sparkfun/SparkFun_Qwiic_6DoF_BMI270/docs/assets/imgs/22397_1.jpg

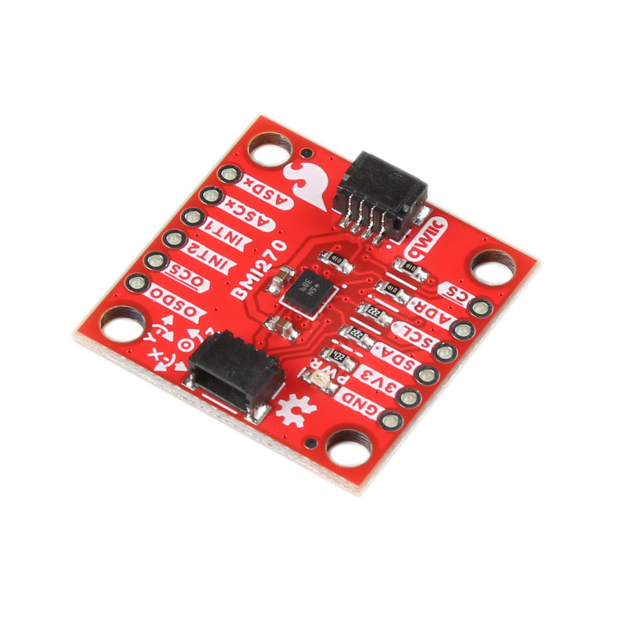
docs/assets/imgs/22397_1.jpg
