sparkfun/SparkFun_Qwiic_6DoF_BMI270/docs/assets/imgs/22397_3.jpg

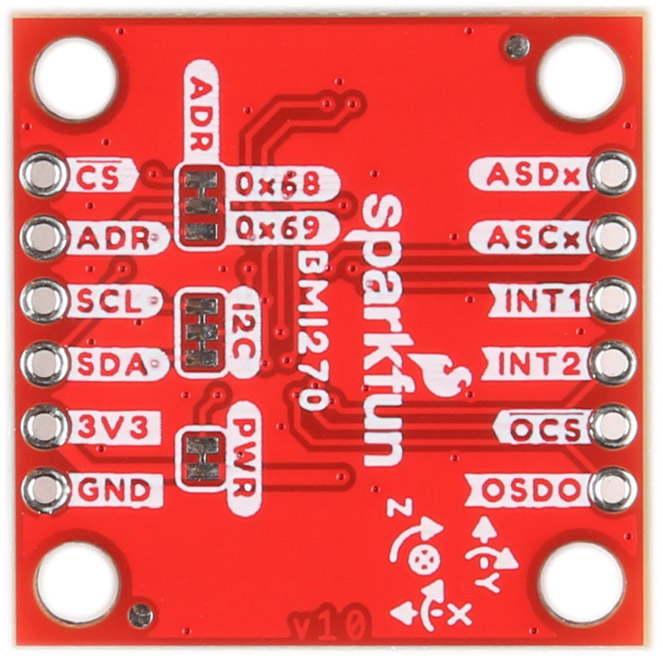
docs/assets/imgs/22397_3.jpg
