sparkfun/SparkFun_Qwiic_6DoF_BMI270/docs/assets/imgs/22398_2.jpg

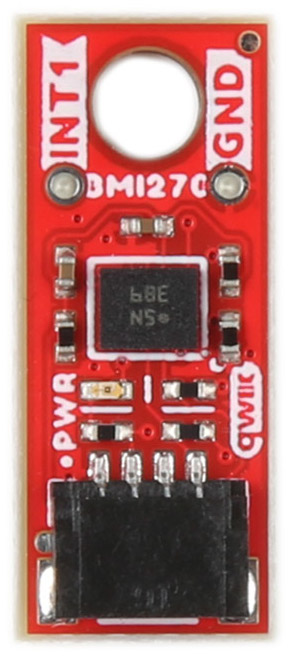
docs/assets/imgs/22398_2.jpg
