sparkfun/SparkFun_Qwiic_6DoF_BMI270/docs/assets/imgs/Qwiic-registered-black.png

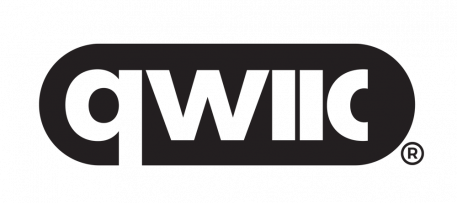
docs/assets/imgs/Qwiic-registered-black.png
